SIDIS17/ADAPTRON/Nouveau dossier/file_00000000715471f59769349c95b38959.png

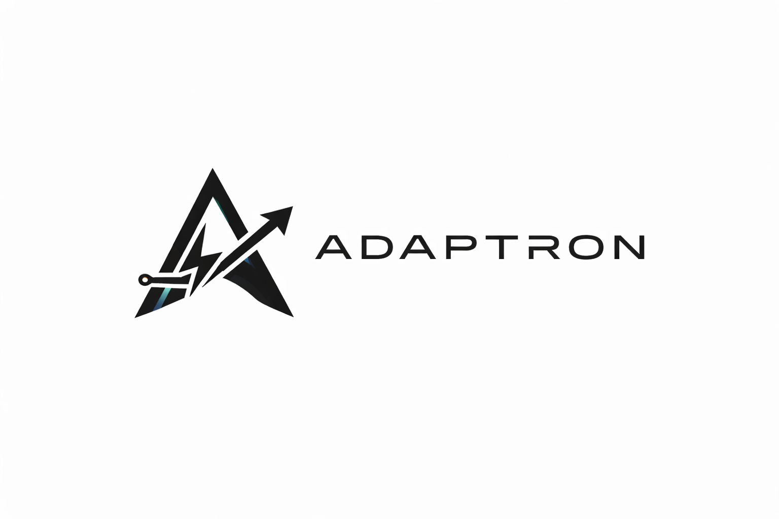
Nouveau dossier/file_00000000715471f59769349c95b38959.png
